michael513823-sys/OpenLapse/STL_files/3D-Print - light_shell_A.STL

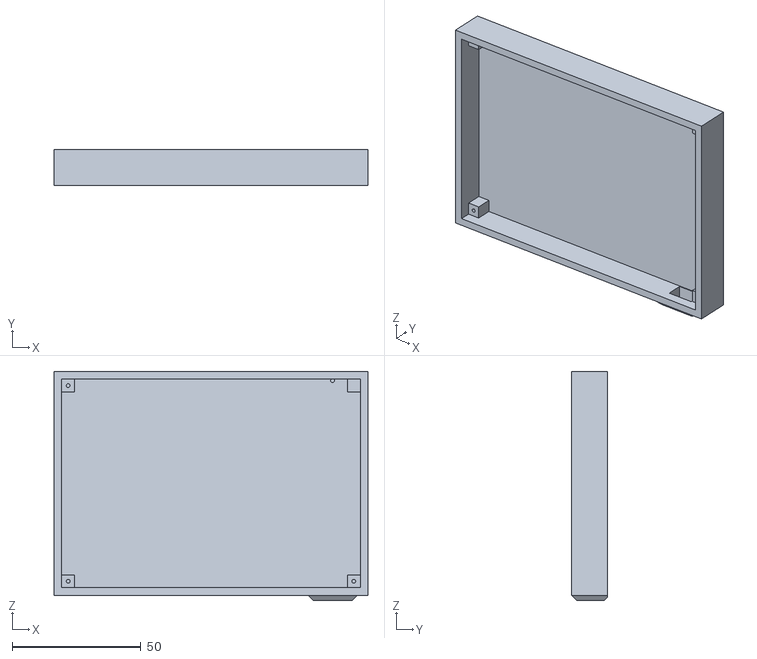
[picture p20: CAD file, 2026-03-29]
STL_files/3D-Print - light_shell_A.STL
122.0 x 14.0 x 89.0
